Adrimapo/taykon/resources/resources_buoyancy/equilibrium_point.png

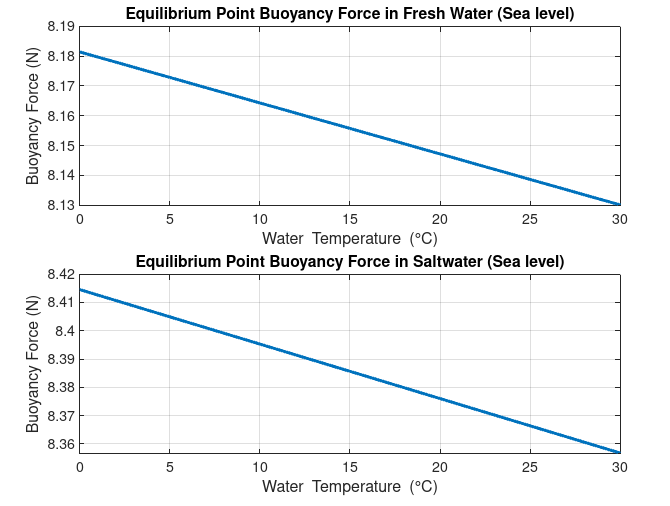
resources/resources_buoyancy/equilibrium_point.png
