Adrimapo/taykon/resources/resources_buoyancy/lift_force.png

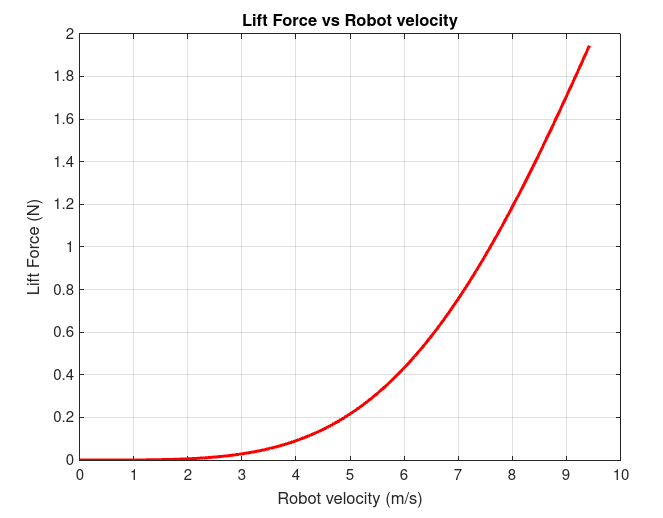
resources/resources_buoyancy/lift_force.png
