Adrimapo/taykon/resources/resources_buoyancy/lift_formula.png

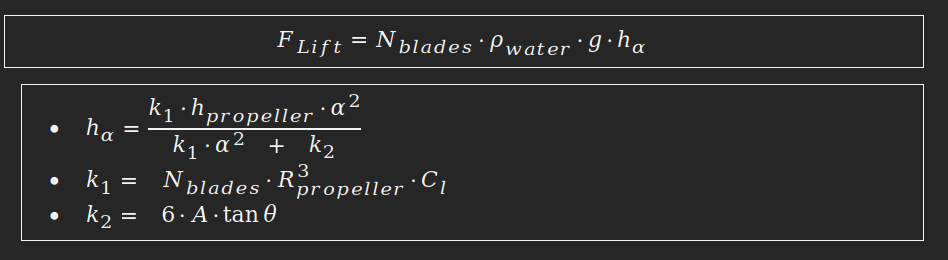
resources/resources_buoyancy/lift_formula.png
