Adrimapo/taykon/resources/resources_buoyancy/velocity_conversion.png

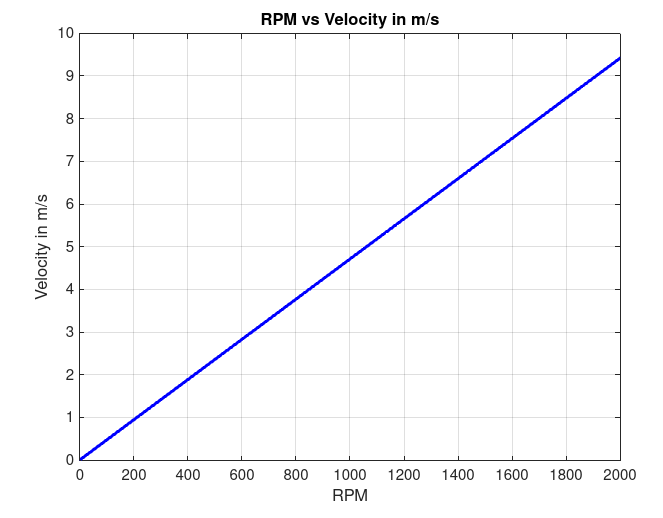
resources/resources_buoyancy/velocity_conversion.png
