Adrimapo/taykon/resources/resources_shell/carcasa-con-tanques.png

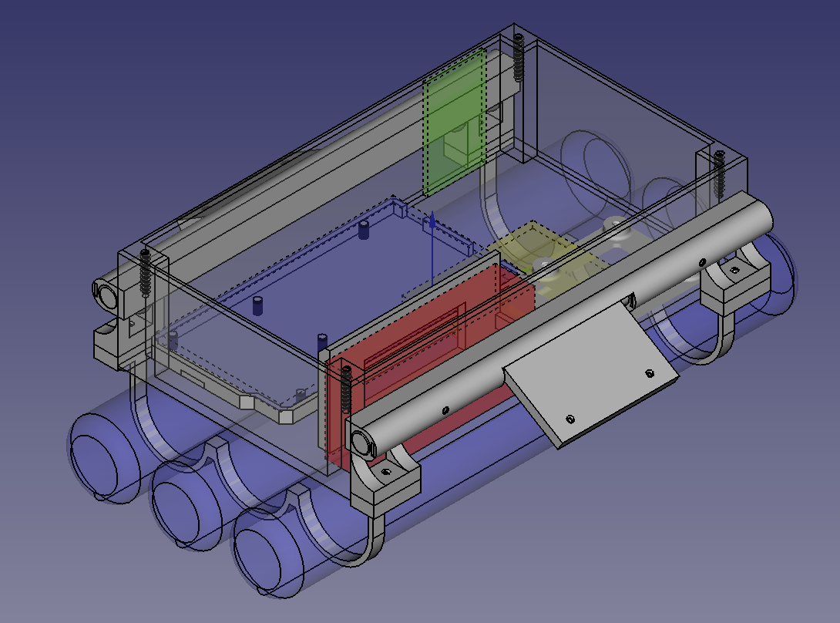
resources/resources_shell/carcasa-con-tanques.png
