Adrimapo/taykon/resources/resources_shell/final-shell-closed.png

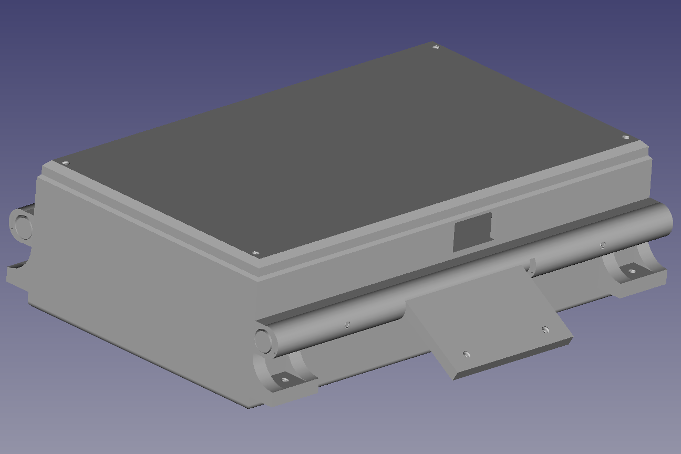
resources/resources_shell/final-shell-closed.png
