Adrimapo/taykon/resources/resources_shell/final-shell.png

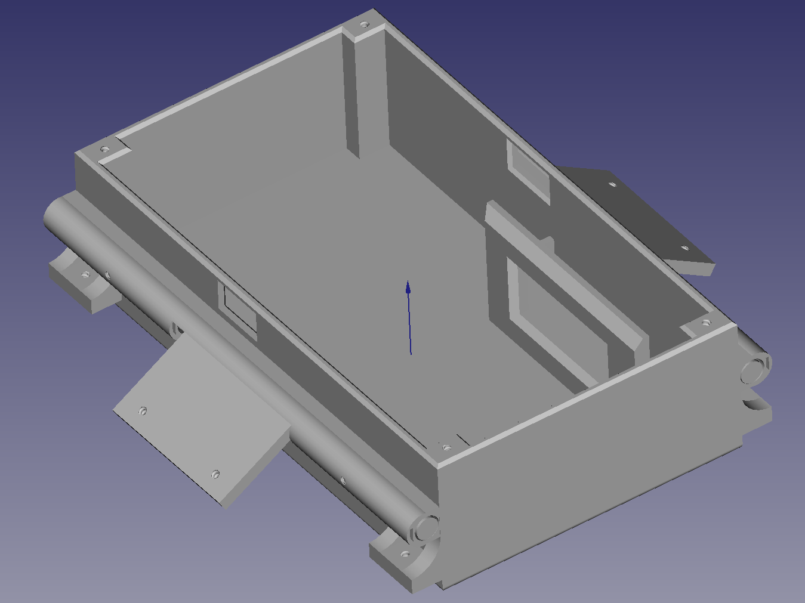
resources/resources_shell/final-shell.png
