Adrimapo/taykon/resources/resources_shell/nueva_tapa_aumentada.png

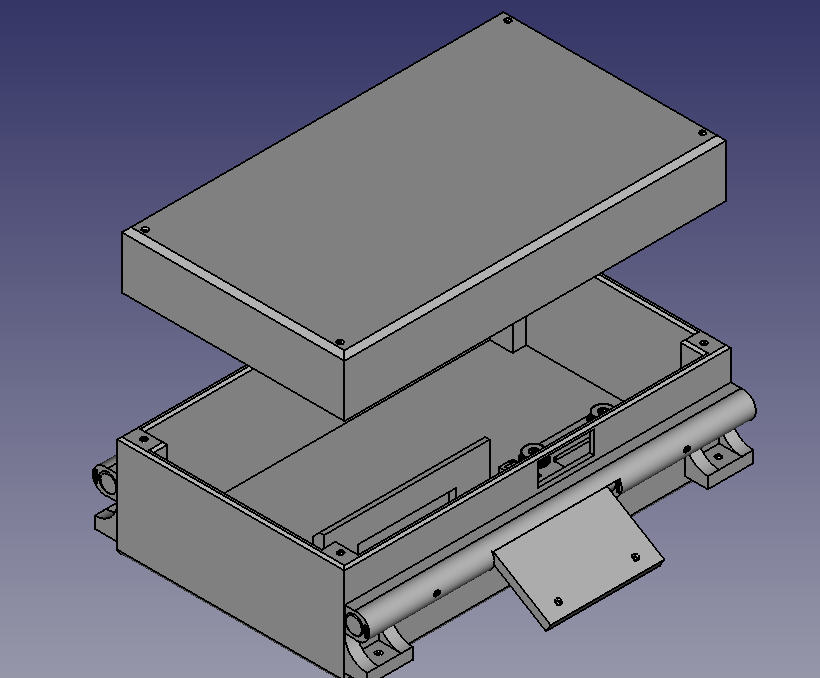
resources/resources_shell/nueva_tapa_aumentada.png
