Adrimapo/taykon/resources/resources_shell/planos-carcasa.png

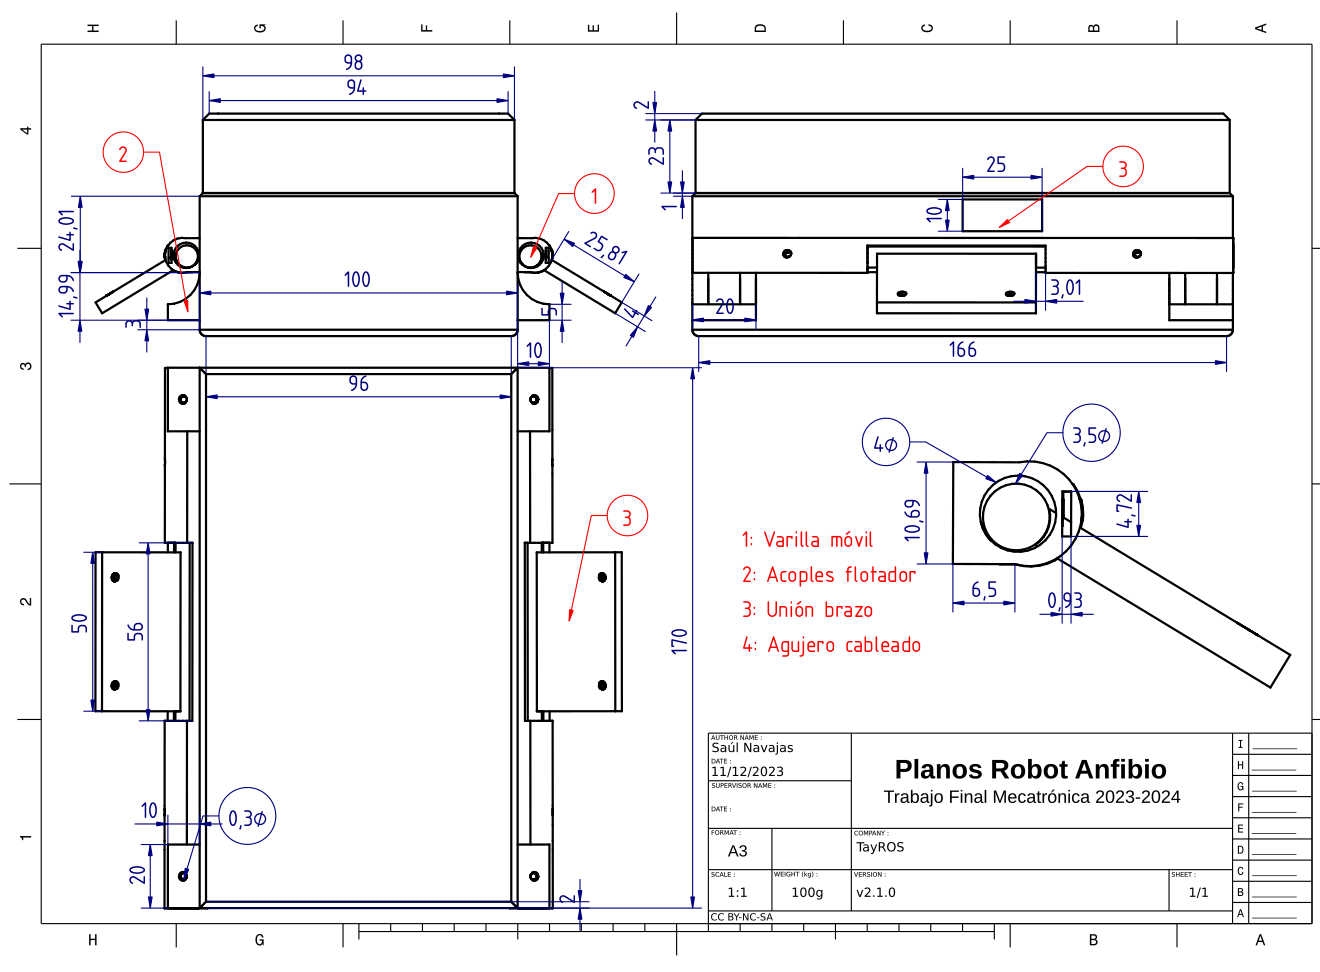
resources/resources_shell/planos-carcasa.png
