Adrimapo/taykon/resources/resources_shell/segunda-version-brazos-reducidos.png

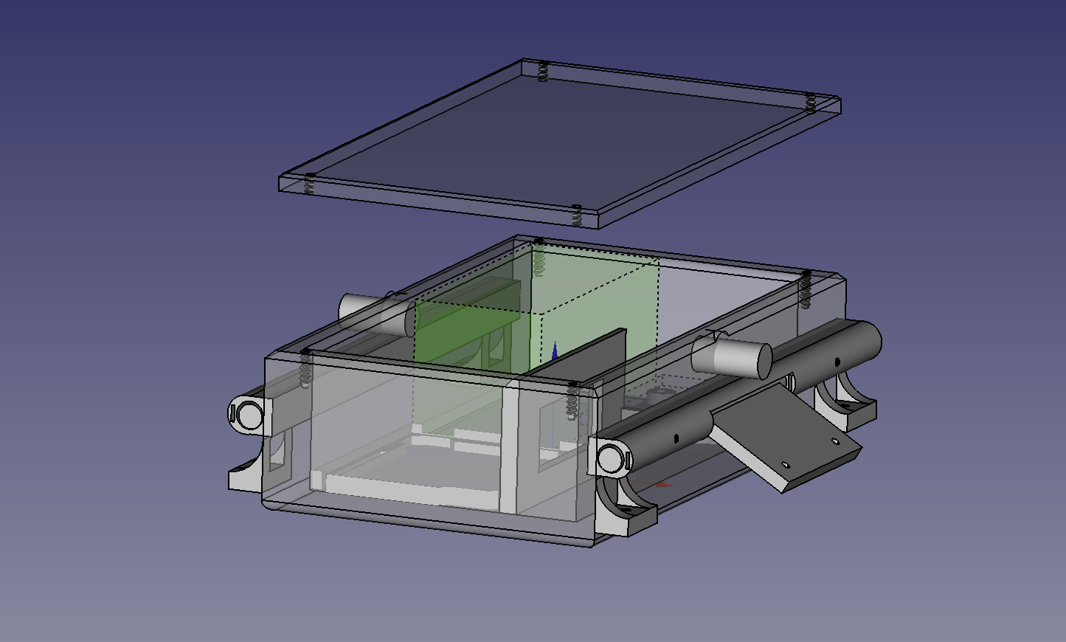
resources/resources_shell/segunda-version-brazos-reducidos.png
