Adrimapo/taykon/resources/resources_shell/sujeccion-tanques.png

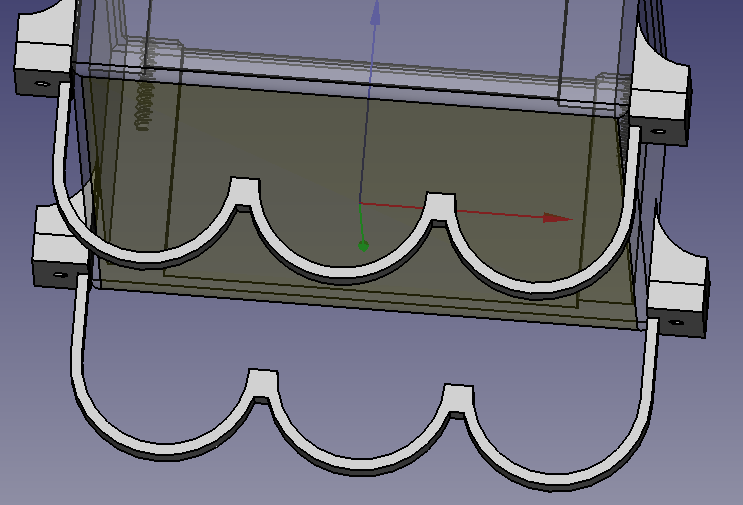
resources/resources_shell/sujeccion-tanques.png
