Adrimapo/taykon/stl/Brazo/tapa_motor.stl

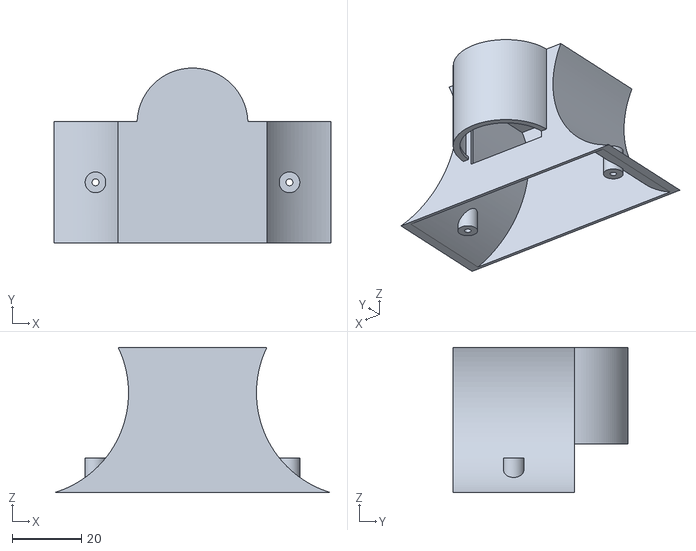
[picture p32: CAD file, 2023-12-13]
stl/Brazo/tapa_motor.stl
80.0 x 50.5 x 42.0
